greenhelix/PortableLidarMapper/hardware/images/print-sample2.png

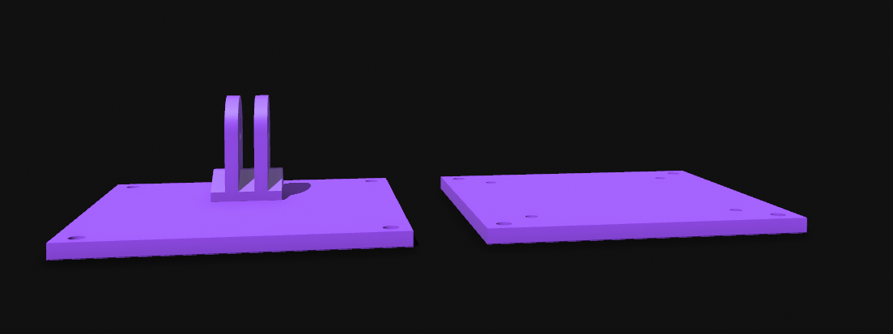
hardware/images/print-sample2.png
